Arunkumar2004/InSpace-CanSat/IMAGE/FPV TRA.jpg

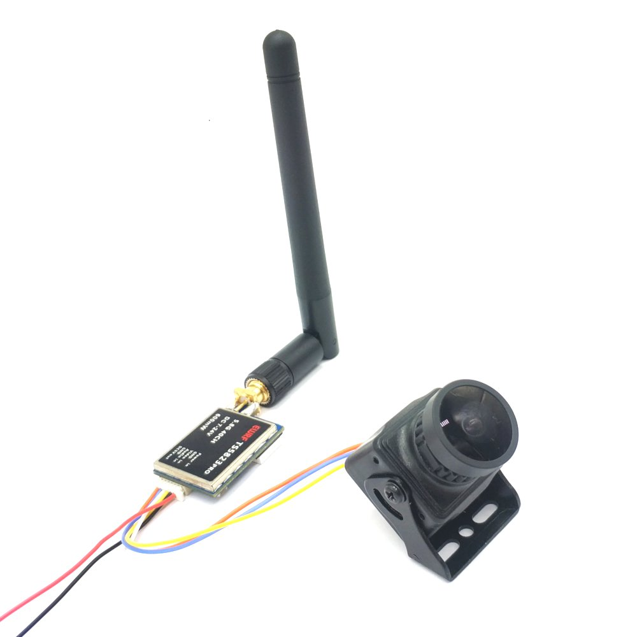
IMAGE/FPV TRA.jpg
