Arunkumar2004/InSpace-CanSat/IMAGE/FPV TRANS.jpg

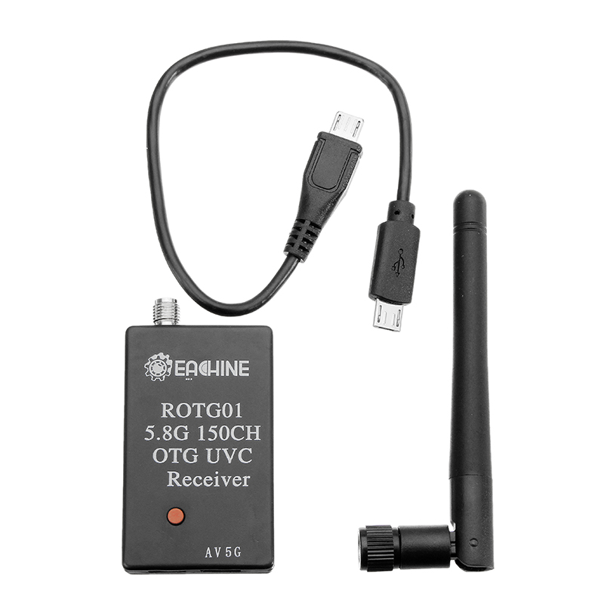
IMAGE/FPV TRANS.jpg
