Arunkumar2004/InSpace-CanSat/IMAGE/General/Assem2.JPG

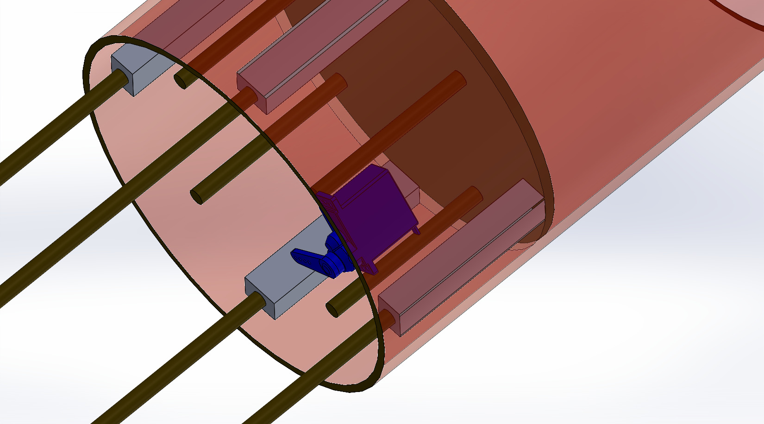
IMAGE/General/Assem2.JPG
