Arunkumar2004/InSpace-CanSat/IMAGE/General/gui model interface.png

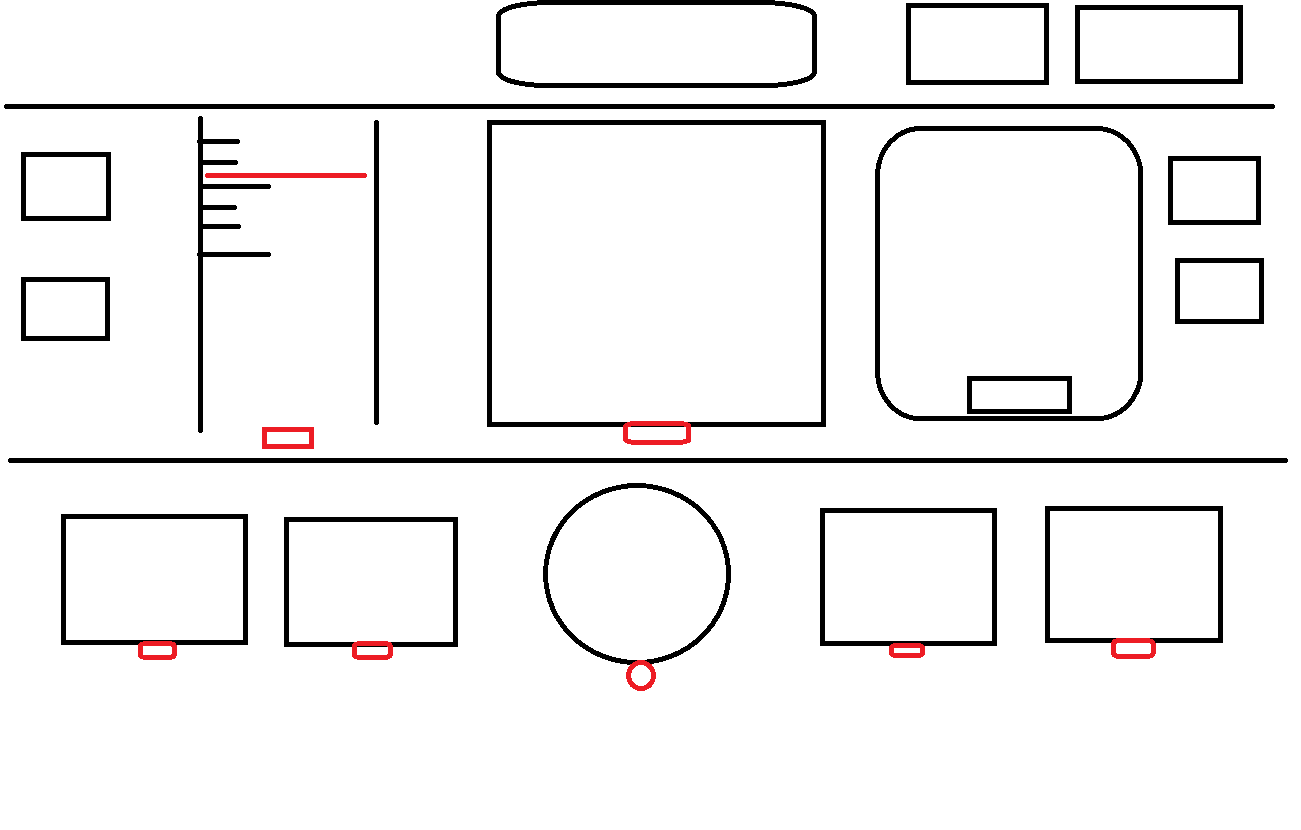
IMAGE/General/gui model interface.png
