Arunkumar2004/InSpace-CanSat/IMAGE/General/para unlocked.png

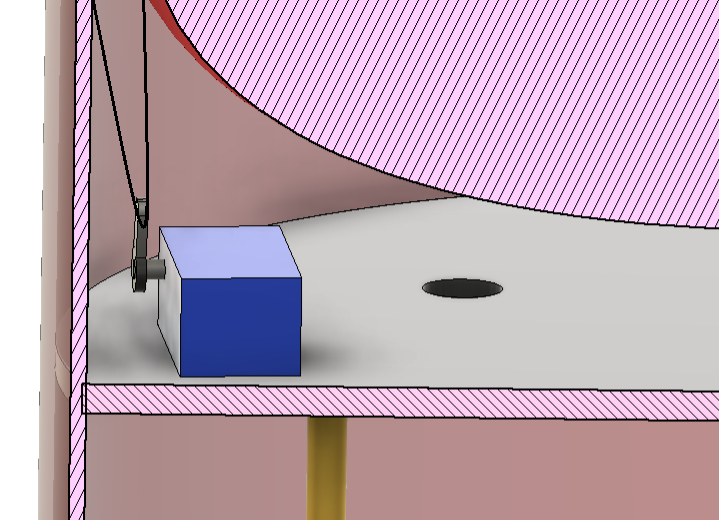
IMAGE/General/para unlocked.png
