Arunkumar2004/InSpace-CanSat/IMAGE/General/paracute pothi.jpg

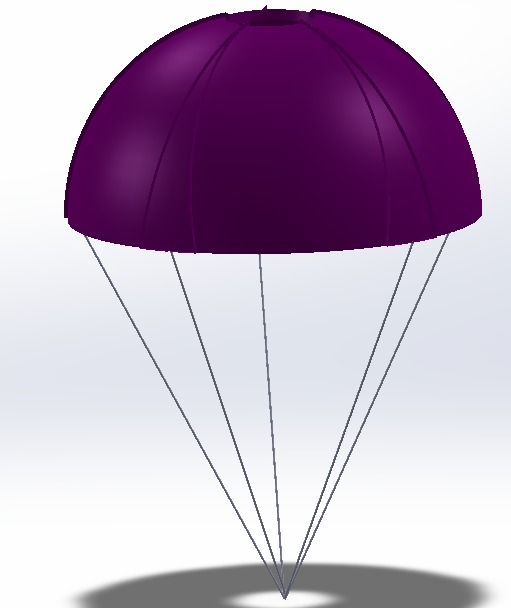
IMAGE/General/paracute pothi.jpg
