Arunkumar2004/InSpace-CanSat/IMAGE/General/Picture1-removebg-preview.png

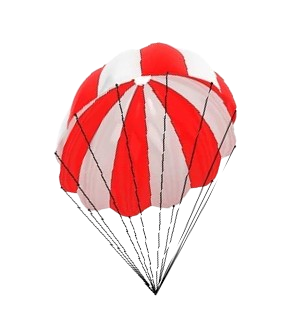
IMAGE/General/Picture1-removebg-preview.png
