Arunkumar2004/InSpace-CanSat/IMAGE/General/Picture2-removebg-preview.png

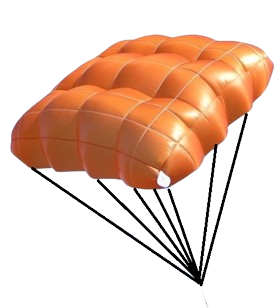
IMAGE/General/Picture2-removebg-preview.png
