Arunkumar2004/InSpace-CanSat/IMAGE/General/WhatsApp Image 2024-09-05 at 16.28.30_a1236e02.jpg

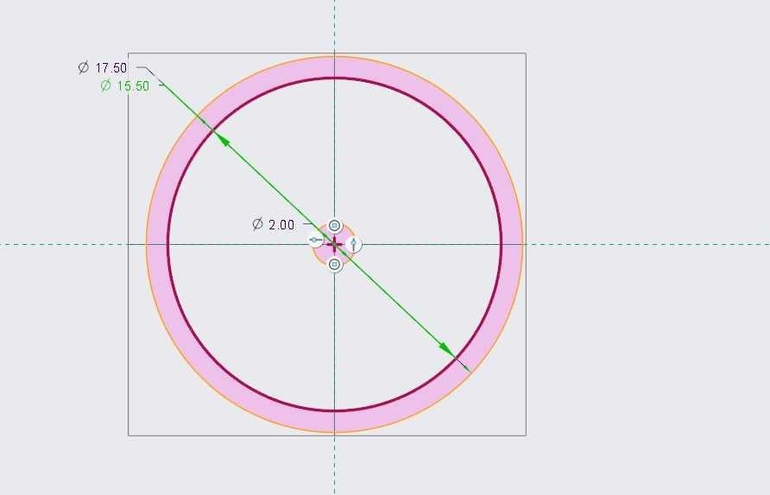
IMAGE/General/WhatsApp Image 2024-09-05 at 16.28.30_a1236e02.jpg
