Arunkumar2004/InSpace-CanSat/IMAGE/General/WhatsApp Image 2024-09-05 at 16.28.31_cf7e8fda.jpg

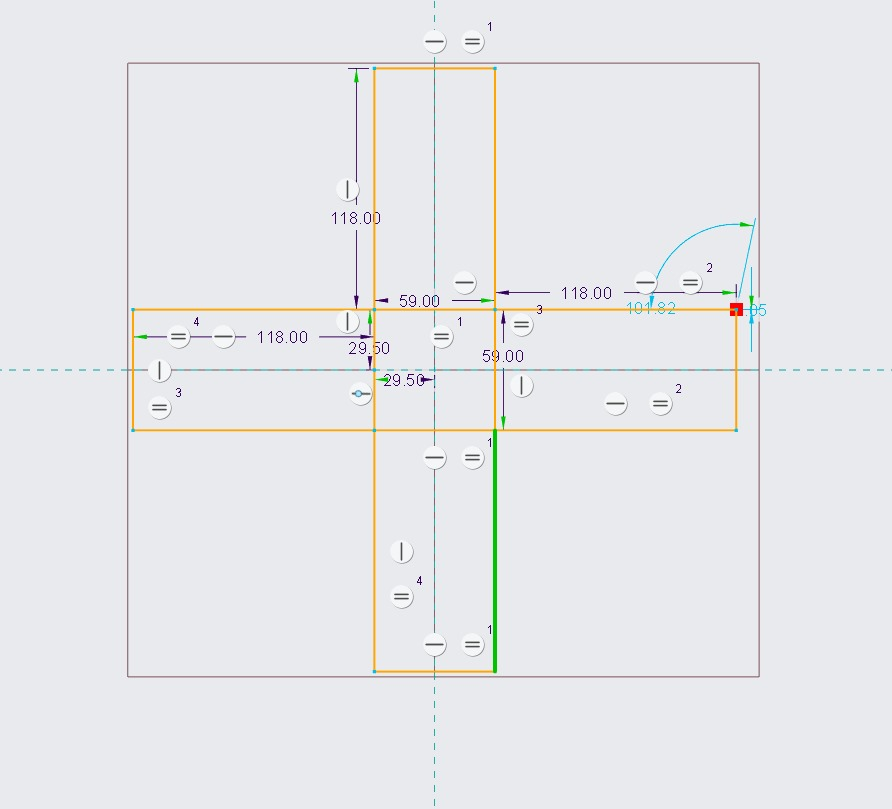
IMAGE/General/WhatsApp Image 2024-09-05 at 16.28.31_cf7e8fda.jpg
