Arunkumar2004/InSpace-CanSat/IMAGE/gyro with payload.png

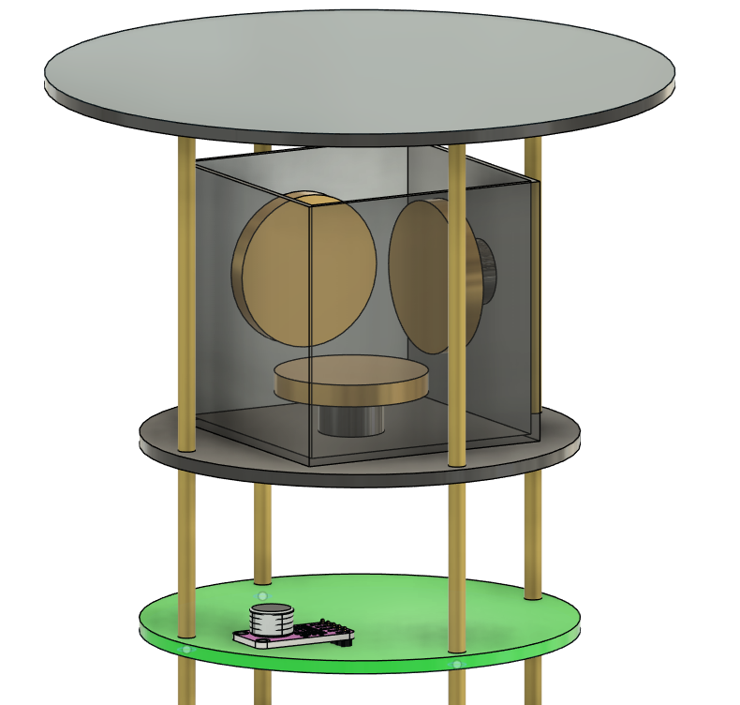
IMAGE/gyro with payload.png
