Arunkumar2004/InSpace-CanSat/IMAGE/pic13.png

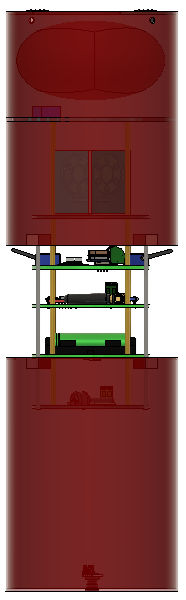
IMAGE/pic13.png
