Arunkumar2004/InSpace-CanSat/IMAGE/pic 1.png

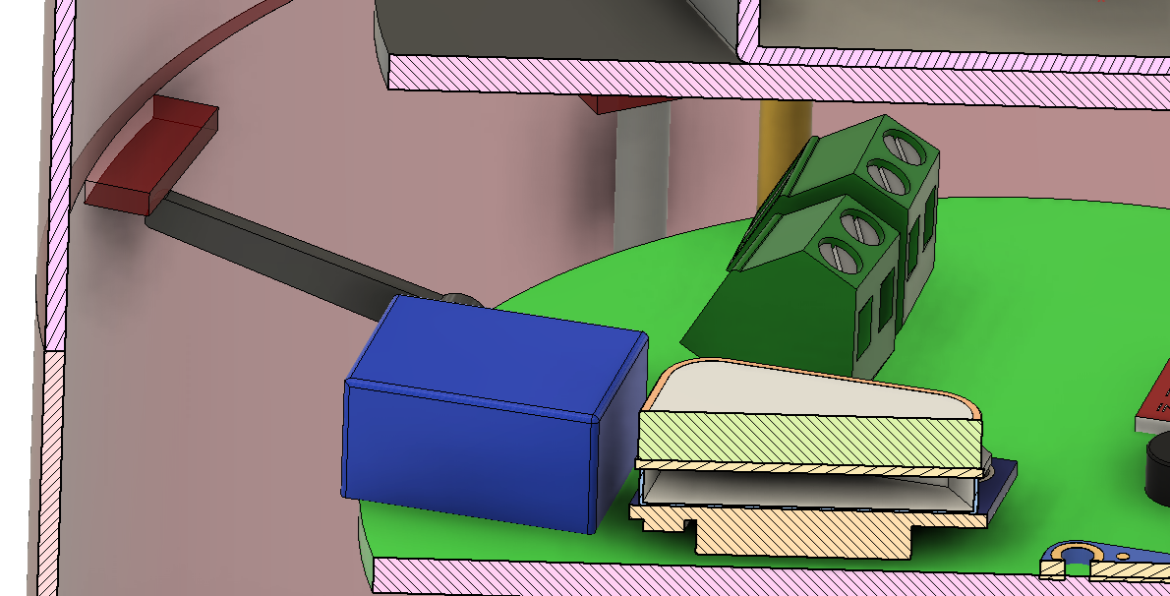
IMAGE/pic 1.png
