Arunkumar2004/InSpace-CanSat/IMAGE/pic 4.png

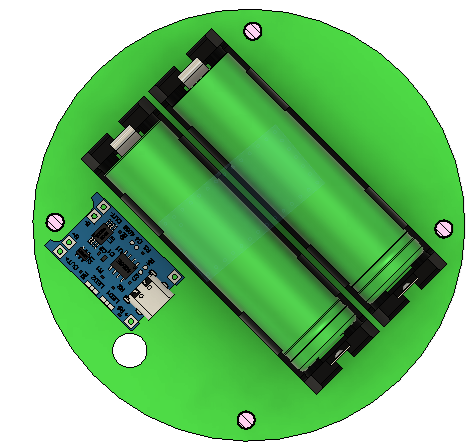
IMAGE/pic 4.png
