Arunkumar2004/InSpace-CanSat/IMAGE/pic 5.png

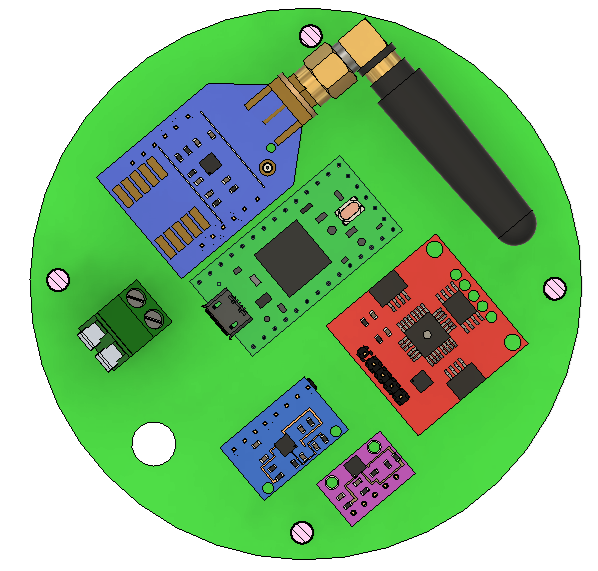
IMAGE/pic 5.png
