Arunkumar2004/InSpace-CanSat/IMAGE/pic 6.png

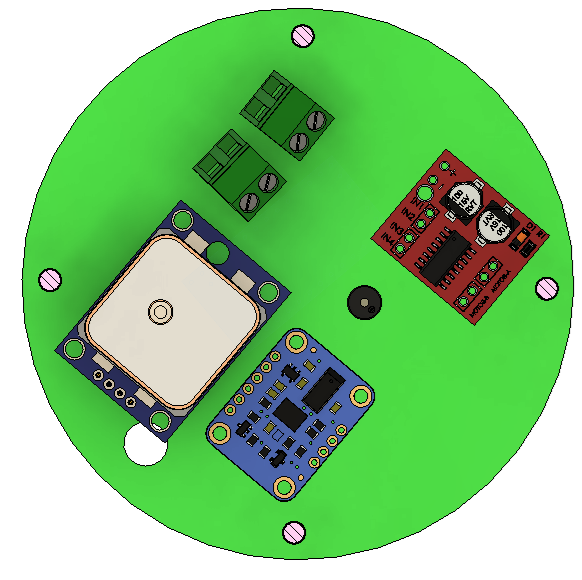
IMAGE/pic 6.png
