Arunkumar2004/InSpace-CanSat/IMAGE/pic 7.png

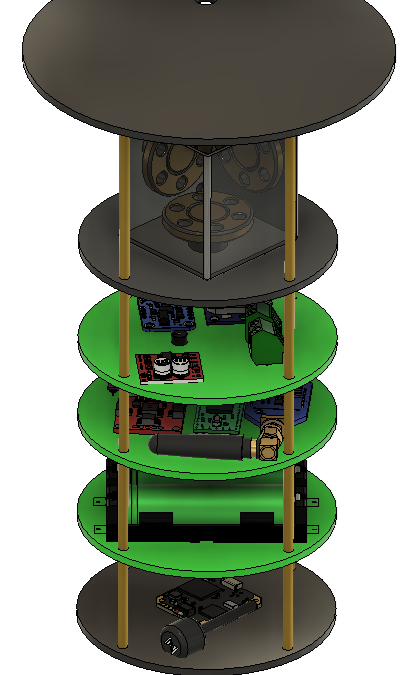
IMAGE/pic 7.png
