Arunkumar2004/InSpace-CanSat/IMAGE/pic 9.png

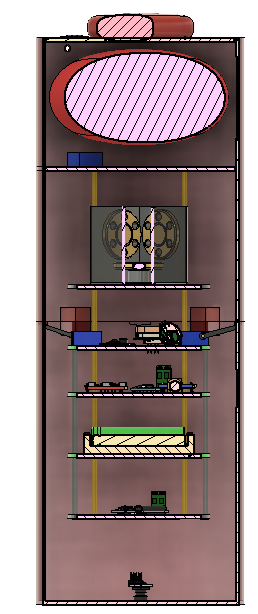
IMAGE/pic 9.png
