Arunkumar2004/InSpace-CanSat/IMAGE/pic 12.png

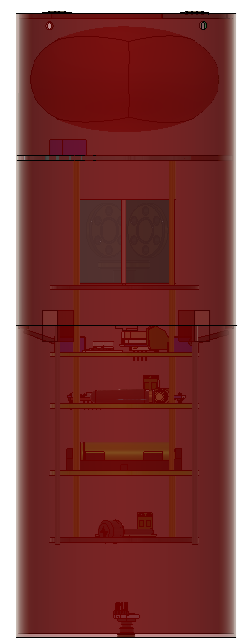
IMAGE/pic 12.png
