Arunkumar2004/InSpace-CanSat/IMAGE/pic 14.png

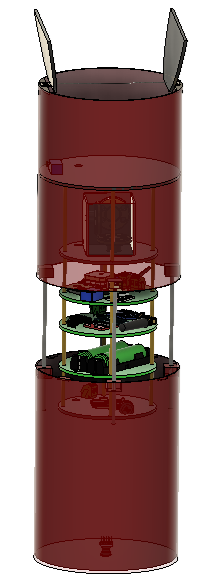
IMAGE/pic 14.png
