Arunkumar2004/InSpace-CanSat/IMAGE/pic 16.png

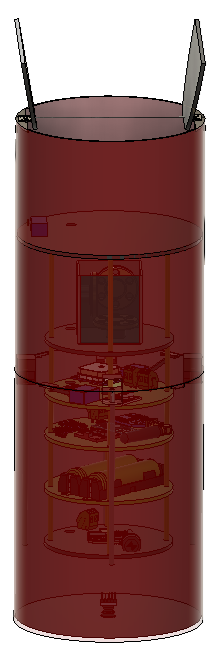
IMAGE/pic 16.png
