Arunkumar2004/InSpace-CanSat/IMAGE/piv 8.png

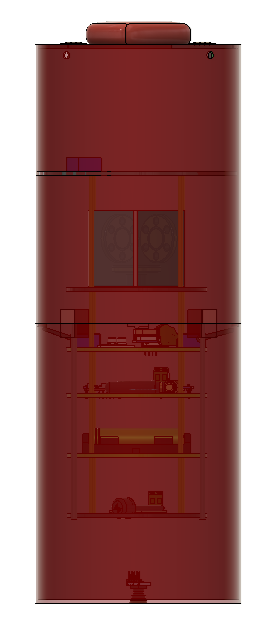
IMAGE/piv 8.png
