Arunkumar2004/InSpace-CanSat/IMAGE/piv 10.png

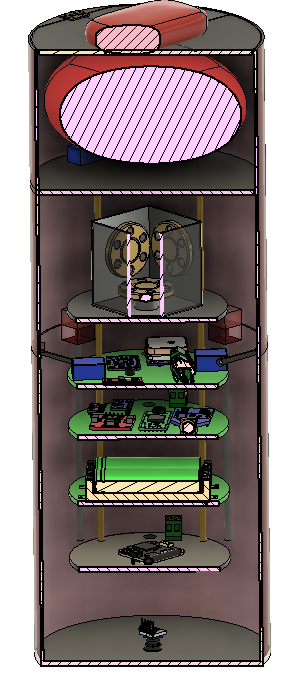
IMAGE/piv 10.png
