Arunkumar2004/InSpace-CanSat/PCB DESIGN/SCH IMAGE/PCB1/PCB1 FRONT 3D.png

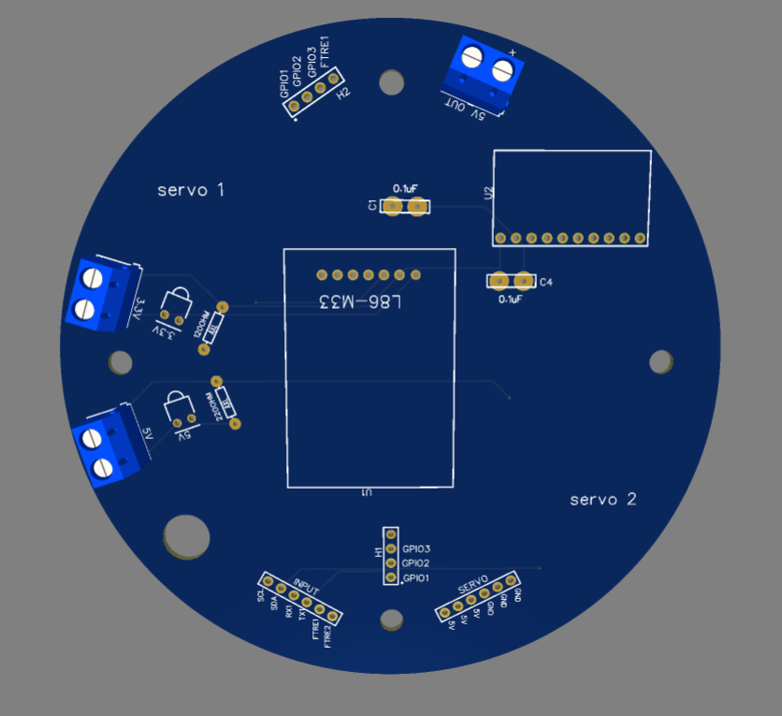
PCB DESIGN/SCH IMAGE/PCB1/PCB1 FRONT 3D.png
