Arunkumar2004/InSpace-CanSat/PCB DESIGN/SCH IMAGE/PCB2/PCB2 BACK 3D.png

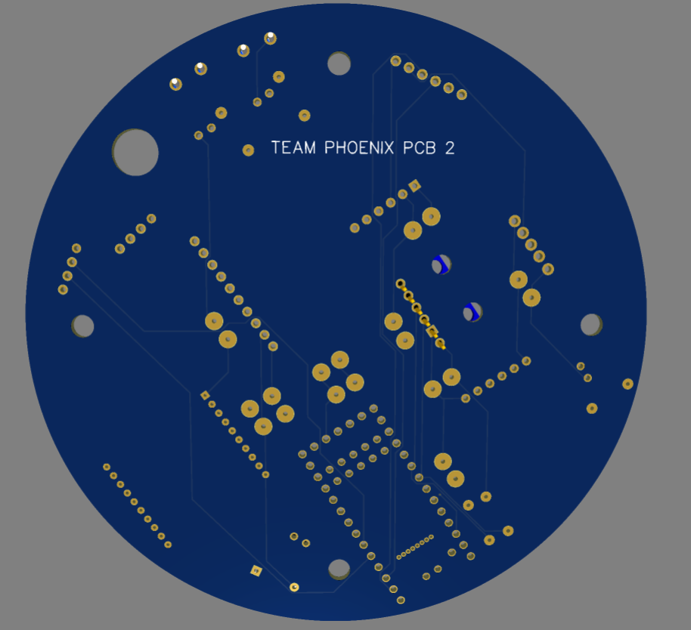
PCB DESIGN/SCH IMAGE/PCB2/PCB2 BACK 3D.png
