Arunkumar2004/InSpace-CanSat/PCB DESIGN/SCH IMAGE/PCB2/PCB2 SCH ROUTE.png

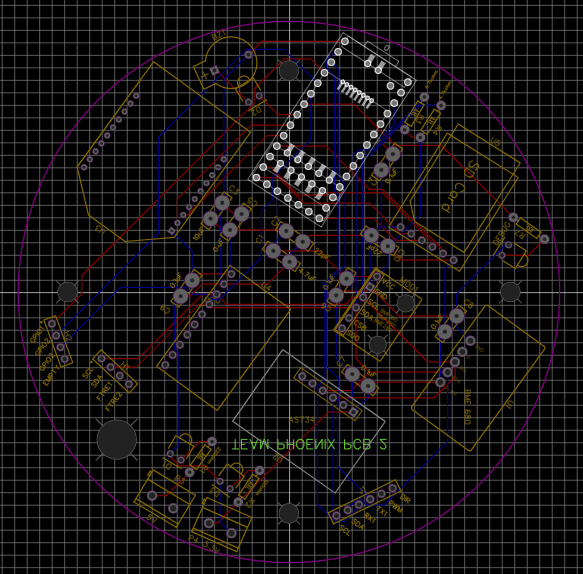
PCB DESIGN/SCH IMAGE/PCB2/PCB2 SCH ROUTE.png
