Arunkumar2004/InSpace-CanSat/PCB DESIGN/SCH IMAGE/PCB3/PCB3 BACK 3D.png

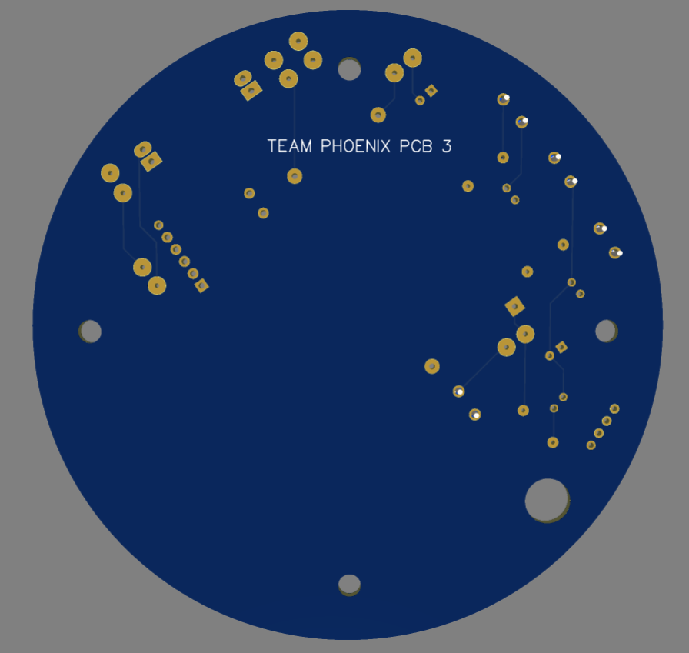
PCB DESIGN/SCH IMAGE/PCB3/PCB3 BACK 3D.png
