Arunkumar2004/InSpace-CanSat/PCB DESIGN/SCH IMAGE/PCB3/PCB3 SCH ROUTE.png

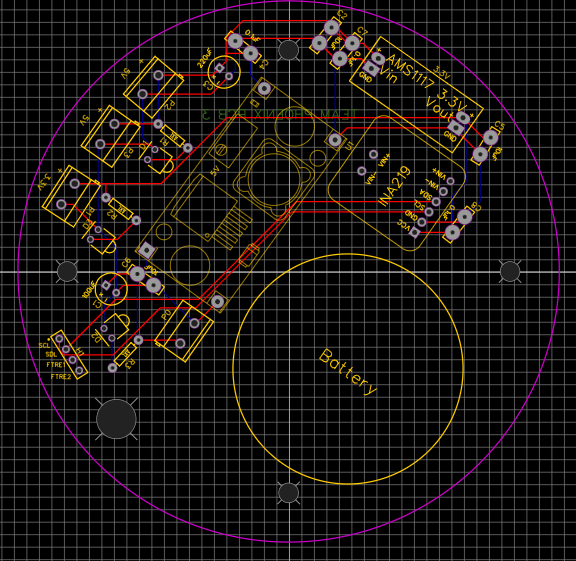
PCB DESIGN/SCH IMAGE/PCB3/PCB3 SCH ROUTE.png
