Arunkumar2004/InSpace-CanSat/PCB DESIGN/SCH IMAGE/PCB3/PCB 3 PHOENIX .png

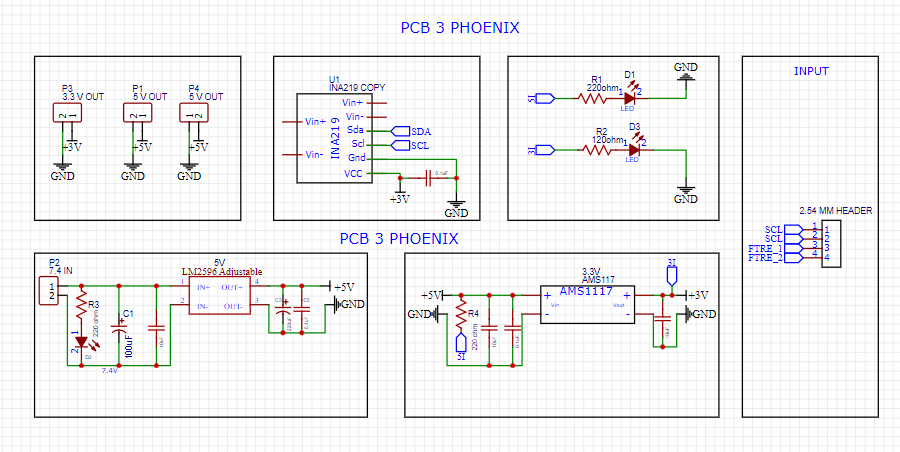
PCB DESIGN/SCH IMAGE/PCB3/PCB 3 PHOENIX .png
